ToanTech/DengFOC_FFBKnob/Src/课时7 蓝牙控制电脑实现/KeyboardTest/lowpass_filter.cpp

#include "lowpass_filter.h"

LowPassFilter::LowPassFilter(float time_constant)
    : Tf(time_constant), y_prev(0.0f)
{
    timestamp_prev = micros();
}

float LowPassFilter::operator()(float x)
{
    unsigned long timestamp = micros();
    float dt = (timestamp - timestamp_prev) * 1e-6f;

    if (dt < 0.0f)
        dt = 1e-3f;
    else if (dt > 0.3f)
    {
        y_prev = x;
        timestamp_prev = timestamp;
        return x;
    }

    float alpha = Tf / (Tf + dt);
    float y = alpha * y_prev + (1.0f - alpha) * x;
    y_prev = y;
    timestamp_prev = timestamp;
    return y;
}
